ynkady/OpenSourceWeatherStation/Software/GSMDataTransmissionGetway/GPRS_MutiSensorforSTM32/User_Clock.c

/******************************************************************************
  Filename:       OSAL_Clock.c
  Revised:        $Date: 2012-03-02 15:52:01 -0800 (Fri, 02 Mar 2012) $
  Revision:       $Revision: 29608 $

  Description:    OSAL Clock definition and manipulation functions.

  Copyright 2008-2012 Texas Instruments Incorporated. All rights reserved.

  IMPORTANT: Your use of this Software is limited to those specific rights
  granted under the terms of a software license agreement between the user
  who downloaded the software, his/her employer (which must be your employer)
  and Texas Instruments Incorporated (the "License"). You may not use this
  Software unless you agree to abide by the terms of the License. The License
  limits your use, and you acknowledge, that the Software may not be modified,
  copied or distributed unless embedded on a Texas Instruments microcontroller
  or used solely and exclusively in conjunction with a Texas Instruments radio
  frequency transceiver, which is integrated into your product. Other than for
  the foregoing purpose, you may not use, reproduce, copy, prepare derivative
  works of, modify, distribute, perform, display or sell this Software and/or
  its documentation for any purpose.

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
  Should you have any questions regarding your right to use this Software,
  contact Texas Instruments Incorporated at www.TI.com.
******************************************************************************/

/*********************************************************************
 * INCLUDES
 */

#include "User_Clock.h"

/*********************************************************************
 * MACROS
 */

#define	YearLength(yr)	((U16)(IsLeapYear(yr) ? 366 : 365))

/*********************************************************************
 * CONSTANTS
 */

#define	BEGYEAR  2000     //  UTC started at 00:00:00 January 1, 2000

#define	DAY      86400UL  // 24 hours * 60 minutes * 60 seconds

/*********************************************************************
 * TYPEDEFS
 */

/*********************************************************************
 * GLOBAL VARIABLES
 */

/*********************************************************************
 * EXTERNAL VARIABLES
 */

/*********************************************************************
 * EXTERNAL FUNCTIONS
 */
/*********************************************************************
 * LOCAL VARIABLES
 */
static U32 previousMacTimerTick = 0;
static U16 remUsTicks = 0;
static U16 timeMSec = 0;

// number of seconds since 0 hrs, 0 minutes, 0 seconds, on the
// 1st of January 2000 UTC
UTCTime OSAL_timeSeconds = 0;

/*********************************************************************
 * LOCAL FUNCTION PROTOTYPES
 */
static U8 monthLength( U8 lpyr, U8 mon );

static void osalClockUpdate( U16 elapsedMSec );



/*********************************************************************
 * @fn      osalClockUpdate
 *
 * @brief   Updates the OSAL Clock time with elapsed milliseconds.
 *
 * @param   elapsedMSec - elapsed milliseconds
 *
 * @return  none
 */
static void osalClockUpdate( U16 elapsedMSec )
{
  // Add elapsed milliseconds to the saved millisecond portion of time
  /*
  timeMSec += elapsedMSec;
  // Roll up milliseconds to the number of seconds
  if ( timeMSec >= 1000 )
  {
    OSAL_timeSeconds += timeMSec / 1000;
    timeMSec = timeMSec % 1000;
  }
  */
  OSAL_timeSeconds+=1;
}

/*********************************************************************
 * @fn      osal_setClock
 *
 * @brief   Set the new time.  This will only set the seconds portion
 *          of time and doesn't change the factional second counter.
 *
 * @param   newTime - number of seconds since 0 hrs, 0 minutes,
 *                    0 seconds, on the 1st of January 2000 UTC
 *
 * @return  none
 */
void osal_setClock( UTCTime newTime )
{
  OSAL_timeSeconds = newTime;
}

/*********************************************************************
 * @fn      osal_getClock
 *
 * @brief   Gets the current time.  This will only return the seconds
 *          portion of time and doesn't include the factional second
 *          counter.
 *
 * @param   none
 *
 * @return  number of seconds since 0 hrs, 0 minutes, 0 seconds,
 *          on the 1st of January 2000 UTC
 */
UTCTime osal_getClock( void )
{
  return ( OSAL_timeSeconds );
}

  /*
   * Updates the OSAL clock and Timers from the MAC 320us timer tick.
   */
void osalTimeUpdate( void )
{
  OSAL_timeSeconds++;
}
/*********************************************************************
 * @fn      osal_ConvertUTCTime
 *
 * @brief   Converts UTCTime to UTCTimeStruct
 *
 * @param   tm - pointer to breakdown struct
 *
 * @param   secTime - number of seconds since 0 hrs, 0 minutes,
 *          0 seconds, on the 1st of January 2000 UTC
 *
 * @return  none
 */
void osal_ConvertUTCTime( UTCTimeStruct *tm, UTCTime secTime )
{
  // calculate the time less than a day - hours, minutes, seconds
  {
    U32 day = secTime % DAY;
    tm->seconds = day % 60UL;
    tm->minutes = (day % 3600UL) / 60UL;
    tm->hour = day / 3600UL;
  }

  // Fill in the calendar - day, month, year
  {
    U16 numDays = secTime / DAY;
    tm->year = BEGYEAR;
    while ( numDays >= YearLength( tm->year ) )
    {
      numDays -= YearLength( tm->year );
      tm->year++;
    }

    tm->month = 0;
    while ( numDays >= monthLength( IsLeapYear( tm->year ), tm->month ) )
    {
      numDays -= monthLength( IsLeapYear( tm->year ), tm->month );
      tm->month++;
    }

    tm->day = numDays;
  }
  tm->day+=1;
  tm->month+=1;
}

/*********************************************************************
 * @fn      monthLength
 *
 * @param   lpyr - 1 for leap year, 0 if not
 *
 * @param   mon - 0 - 11 (jan - dec)
 *
 * @return  number of days in specified month
 */
static U8 monthLength( U8 lpyr, U8 mon )
{
  U8 days = 31;

	if ( mon == 1 ) // feb
  {
		days = ( 28 + lpyr );
  }
  else
  {
    if ( mon > 6 ) // aug-dec
    {
      mon--;
    }

    if ( mon & 1 )
    {
      days = 30;
    }
  }

	return ( days );
}

/*********************************************************************
 * @fn      osal_ConvertUTCSecs
 *
 * @brief   Converts a UTCTimeStruct to UTCTime
 *
 * @param   tm - pointer to provided struct
 *
 * @return  number of seconds since 00:00:00 on 01/01/2000 (UTC)
 */
UTCTime osal_ConvertUTCSecs( UTCTimeStruct *tm )
{
  U32 seconds;
  tm->day-=1;
  tm->month-=1;
  /* Seconds for the partial day */
  seconds = (((tm->hour * 60UL) + tm->minutes) * 60UL) + tm->seconds;

  /* Account for previous complete days */
  {
    /* Start with complete days in current month */
    U16 days = tm->day;

    /* Next, complete months in current year */
    {
      signed int month = tm->month;
      while ( --month >= 0 )
      {
        days += monthLength( IsLeapYear( tm->year ), month );
      }
    }

    /* Next, complete years before current year */
    {
      U16 year = tm->year;
      while ( --year >= BEGYEAR )
      {
        days += YearLength( year );
      }
    }

    /* Add total seconds before partial day */
    seconds += (days * DAY);
  }
  return ( seconds );
}
