ynkady/OpenSourceWeatherStation/Software/ThermoscreenMutiSensors/Multi-in-one_sensor1.0/HTU21D.h

/* 
 HTU21D Humidity Sensor Library
 By: Nathan Seidle
 SparkFun Electronics
 Date: September 22nd, 2013
 License: This code is public domain but you buy me a beer if you use this and we meet someday (Beerware license).
 
 Get humidity and temperature from the HTU21D sensor.
 
 */
 

#if defined(ARDUINO) && ARDUINO >= 100
 #include "Arduino.h"
#else
 #include "WProgram.h"
#endif


#define HTDU21D_ADDRESS 0x40  //Unshifted 7-bit I2C address for the sensor

#define TRIGGER_TEMP_MEASURE_HOLD  0xE3
#define TRIGGER_HUMD_MEASURE_HOLD  0xE5
#define TRIGGER_TEMP_MEASURE_NOHOLD  0xF3
#define TRIGGER_HUMD_MEASURE_NOHOLD  0xF5
#define WRITE_USER_REG  0xE6
#define READ_USER_REG  0xE7
#define SOFT_RESET  0xFE

class HTU21D {

public:
  HTU21D();

  //Public Functions
  bool begin();
  float readHumidity(void);
  float readTemperature(void);
  void setResolution(byte resBits);

  //Public Variables

private:
  //Private Functions

  byte read_user_register(void);
  byte check_crc(uint16_t message_from_sensor, uint8_t check_value_from_sensor);

  //Private Variables

};
